scrotumLab/RadioMusic-for-BugBrand-FRAC/RadioMusic/SDPlayPCM.cpp

/* Audio Library for Teensy 3.X
 * Copyright (c) 2014, Paul Stoffregen, paul@pjrc.com
 *
 * Development of this audio library was funded by PJRC.COM, LLC by sales of
 * Teensy and Audio Adaptor boards.  Please support PJRC's efforts to develop
 * open source software by purchasing Teensy or other PJRC products.
 *
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
 * THE SOFTWARE IS PROVIDED "AS IS", WITHOUT WARRANTY OF ANY KIND, EXPRESS OR
 * IMPLIED, INCLUDING BUT NOT LIMITED TO THE WARRANTIES OF MERCHANTABILITY,
 * FITNESS FOR A PARTICULAR PURPOSE AND NONINFRINGEMENT. IN NO EVENT SHALL THE
 * AUTHORS OR COPYRIGHT HOLDERS BE LIABLE FOR ANY CLAIM, DAMAGES OR OTHER
 * LIABILITY, WHETHER IN AN ACTION OF CONTRACT, TORT OR OTHERWISE, ARISING FROM,
 * OUT OF OR IN CONNECTION WITH THE SOFTWARE OR THE USE OR OTHER DEALINGS IN
 * THE SOFTWARE.
 */

#include "SDPlayPCM.h"

#include "spi_interrupt.h"
#include "RadioMusic.h"

#ifdef DEBUG_PCM_PLAYER
#define D(x) x
#else
#define D(x)
#endif

#ifdef DEBUG_AUDIO_BUFFER
#define B(x) x
#else
#define B(x)
#endif


void SDPlayPCM::begin(void) {
//	AudioStartUsingSPI();
	playing = false;
	finished = false;
	errors = 0;
	// Set a dummy filename so it doesn't match anything at startup.
	filename = "--------";
}

void SDPlayPCM::loopPlayback(bool loop) {
	__disable_irq()
	;
	looping = loop;
	__enable_irq()
	;
}

bool SDPlayPCM::changeFileTo(AudioFileInfo* info, bool closeFirst) {
	filename = info->name;
//	AudioStopUsingSPI();
	__disable_irq()
	;
	if (closeFirst) {
		rawfile.close();
	}
	rawfile = SD.open(info->name.c_str());

	dataSize = info->size;
	bytesLeftInFile = info->size;
	dataOffset = info->dataOffset;
	channels = info->getChannels();
	bytesPerSample = info->getBytesPerSample();
	sampleRateSpeed = (float) info->getSampleRate() / 44100.0;
	bytesAvailable = 0;
	readPositionInBytes = 0;
	bufferFillPosition = 0;
	finished = false;
	readError = false;
	__enable_irq()
	;
//	AudioStartUsingSPI();
	D(
		if (dataSize % bytesPerSample != 0) {
			debugHeader();
			Serial.print("!!!! Data size not aligned : ");
			Serial.print(dataSize);
		}
		if(info->startPlayFrom != 0) {
			Serial.print("!!! Start play from is not 0 : ");
			Serial.println(info->startPlayFrom);
		}
		debugHeader();
		Serial.print("Change File To ");
		Serial.print(info->name);
		Serial.print(". BPS ");
		Serial.print(bytesPerSample);
		Serial.print(". BLIF ");
		Serial.print(bytesLeftInFile);
		Serial.print(" .SampleRateSpeed ");
		Serial.print(sampleRateSpeed);
		Serial.print(" .Bytes Per Block ");
		Serial.println(
				ceil(AUDIO_BLOCK_SAMPLES * speed * bytesPerSample * channels));
	);
	return true;
}

bool SDPlayPCM::skipTo(uint32_t dataPosition) {
	if(!rawfile) return false;
	uint32_t pos = dataOffset + dataPosition;
	AudioStopUsingSPI();
	__disable_irq()
	;
	boolean didseek = rawfile.seek(pos);
	bytesLeftInFile = dataSize - dataPosition;
	readPositionInBytes = 0;
	bytesAvailable = 0;
	bufferFillPosition = 0;
	readError = false;
	playing = true;
	finished = false;
	__enable_irq()
	;
	AudioStartUsingSPI();
	if(!didseek) {
		D(
			debugHeader();
			Serial.println("!!! didseek is false");
		);
		return false;
	}
	return true;
}

bool SDPlayPCM::playFrom(AudioFileInfo* info) {

	uint32_t pos = info->dataOffset + info->startPlayFrom;

	D(
		debugHeader();
		Serial.print("Play ");
		Serial.print(info->name);
		Serial.print(" from ");
		Serial.print(info->startPlayFrom);
		Serial.print(" starting from ");
		Serial.println(pos);
	);


	// We use the same file, just seek inside it.
	if (info->name.compareTo(filename) == 0) {
		D(
			debugHeader();
			Serial.print("Continuing on file ");
			Serial.print(filename);
			Serial.print(" from ");
			Serial.print(info->startPlayFrom);
			Serial.print(" of ");
			Serial.print(info->size);
			Serial.print(" with ");
			Serial.print(info->getBytesPerSample());
			Serial.print(" bps. File size ");
			Serial.println(rawfile.size());
		);

		updateRequired = false;
		return skipTo(info->startPlayFrom);

	} else {
		D(
			Serial.print("Different name ");
			Serial.println(filename);
		);
	}

	//if(playing) stop();

//	if(!playing) AudioStartUsingSPI();

	if (!changeFileTo(info, true)) {
		updateRequired = false;
		return false;
	} else {
		D(
			debugHeader();
			Serial.print("Change OK : ");
			Serial.println(rawfile.name());
		);
	}

	skipTo(info->startPlayFrom);

//	__disable_irq()
//	;
//	if(!rawfile.seek(pos)) {
//		debugHeader();
//		Serial.println("Seek failed");
//	}
//	bytesLeftInFile = info->size - info->startPlayFrom;
//	playing = true;
//	finished = false;
//	__enable_irq()
//	;

	D(
		debugHeader();
		Serial.print("Open. RPIB ");
		Serial.print(readPositionInBytes);
		Serial.print(" .InfoSize ");
		Serial.print(info->size);
		Serial.print(" .BLIF ");
		Serial.print(bytesLeftInFile);
		Serial.print(". File pos ");
		Serial.print(rawfile.position());
		Serial.print(". File size ");
		Serial.print(rawfile.size());
		Serial.print(". Avail ");
		Serial.println(fileAvailable());
	);
	updateRequired = false;
	return true;
}

void SDPlayPCM::restart() {

	D(
		debugHeader();
		Serial.println("Restart");
	);
	__disable_irq()
	;
	rawfile.seek(dataOffset);
	bytesLeftInFile = dataSize;
	playing = true;
	finished = false;
	__enable_irq()
	;
}

void SDPlayPCM::stop(void) {
	__disable_irq()
	;
	D(
		debugHeader();
		Serial.println("Stop");
	);
	if (playing) {
		playing = false;
		__enable_irq()
		;
//		AudioStopUsingSPI();
	} else {
		__enable_irq()
		;
	}
}

void SDPlayPCM::update(void) {

	uint16_t n = AUDIO_BLOCK_SAMPLES;
	audio_block_t *block;
	uint16_t i = 0;

	if(errors > 100) return;

	// only update if we're playing
	if (!playing)
		return;

	if(!looping) {
		if(finished || bytesLeftInFile == 0) {
			D(
				debugHeader();
				Serial.println("File finished");
			);
			playing = false;
			finished = true;
			return;
		}
	}

	// allocate the audio blocks to transmit
	block = allocate();
	if (block == NULL)
		return;

	inUpdate = true;
	read = 0;
	speed = playbackSpeed * sampleRateSpeed;
	bytesRequired = ceil(AUDIO_BLOCK_SAMPLES * speed) * bytesPerSample * channels;

	if (bytesRequired > AUDIOBUFSIZE) {
		bytesRequired = AUDIOBUFSIZE;
		D(
			debugHeader();
			Serial.println("!!! Bytes Required is bigger than the audio buffer..");
		);
	}

	if (bytesAvailable < bytesRequired) {

		bool bufferReadOk = false;
		if (bytesRequired
				< AUDIO_BLOCK_SAMPLES * bytesPerSample * channels) {
			bufferReadOk = fillBuffer(AUDIO_BLOCK_SAMPLES * bytesPerSample * channels);
		} else {
			bufferReadOk = fillBuffer(bytesRequired);
		}
B(
		if (read % bytesPerSample != 0) {
			debugHeader();
			Serial.print("Read not aligned ");
			Serial.print(read % bytesPerSample);
			Serial.print("\t");
			Serial.print(read);
			Serial.print("\t");
			Serial.println(bytesRequired);
		}
);

		if (read >= 0 && read < bytesRequired) {
			B(
				if (bytesAvailable % bytesPerSample != 0)
				{
					debugHeader();
					Serial.println("Bytes available not aligned");
				}

				if (read % bytesPerSample != 0) {
					debugHeader();
					Serial.print("Read not aligned ");
					Serial.print(read % bytesPerSample);
					Serial.print("\t");
					Serial.print(read);
					Serial.print("\t");
					Serial.println(bytesRequired);
				}
				if(!finished) {
					debugHeader();
					Serial.print("Not enough data from fill buffer ");
					Serial.print(bytesRequired);
					Serial.print("\t");
					Serial.print(bytesAvailable);
					Serial.print("\t");
					Serial.println(fileAvailable());
				} else {
					debugHeader();
					Serial.print("File finished ");
					Serial.print(bytesRequired);
					Serial.print("\t");
					Serial.print(bytesAvailable);
					Serial.print("\t");
					Serial.println(fileAvailable());
				}
			);
			n = min(AUDIO_BLOCK_SAMPLES,
					floor(bytesAvailable / (bytesPerSample * channels))	/ speed);
		} else if (readError || !bufferReadOk) {
			D(Serial.print("Read error. ");Serial.println(errors););
			errors++;
			readError = false;
			// Fill block with zero.
			for (i = 0; i < AUDIO_BLOCK_SAMPLES; i++) {
				block->data[i] = 0;
			}
			transmit(block);
			release(block);
			updates++;
			return;
		}

	}

	int16_t* out = block->data;

	l0 = 0;
	lowSamplePos = 0;
	float sp = speed * channels;

	// Check for buffer wrapping here so we don't do it 128 times in the loop.
	boolean bufferWrap = ((n*sp) * bytesPerSample) + readPositionInBytes >= AUDIOBUFSIZE;
	if (bytesPerSample == 2) {
		// 16 bit copy
		if(bufferWrap) {
			for (i = 0; i < n; i++) {
				lowSamplePos = (i * speed);
				l0 = readPositionInBytes + (lowSamplePos << channels);
				if (l0 >= AUDIOBUFSIZE) l0 -= AUDIOBUFSIZE;
				memcpy(out++, &audioBuffer[l0],2);
			}
		} else {
			// We won't wrap the buffer edge so don't check
			for (i = 0; i < n; i++) {
				lowSamplePos = (i * speed);
				l0 = readPositionInBytes + (lowSamplePos << channels);
				memcpy(out++, &audioBuffer[l0],2);
			}
		}
	} else if (bytesPerSample == 3) {

		if(channels == 1) {
			if(bufferWrap) {
				// 24 bit copy.
				for (i = 0; i < n; i++) {
					lowSamplePos = (i * speed);
					l0 = readPositionInBytes + (lowSamplePos * 3);
					if (l0 >= AUDIOBUFSIZE) l0 -= AUDIOBUFSIZE;
					*out++ = (audioBuffer[l0] | (audioBuffer[++l0] << 8) | (audioBuffer[++l0] << 16)) >> 8;
				}
			} else {
				// 24 bit copy.
				for (i = 0; i < n; i++) {
					lowSamplePos = (i * speed);
					l0 = readPositionInBytes + (lowSamplePos * 3);
					*out++ = (audioBuffer[l0] | (audioBuffer[++l0] << 8) | (audioBuffer[++l0] << 16)) >> 8;
				}
			}
		} else {
			if(bufferWrap) {
				// 24 bit copy.
				for (i = 0; i < n; i++) {
					lowSamplePos = (i * speed);
					l0 = readPositionInBytes + ((lowSamplePos * 3) << 1);
					if (l0 >= AUDIOBUFSIZE) l0 -= AUDIOBUFSIZE;
					*out++ = (audioBuffer[l0] | (audioBuffer[++l0] << 8) | (audioBuffer[++l0] << 16)) >> 8;
				}
			} else {
				// 24 bit copy.
				for (i = 0; i < n; i++) {
					lowSamplePos = (i * speed);
					l0 = readPositionInBytes + ((lowSamplePos * 3) << 1);
					*out++ = (audioBuffer[l0] | (audioBuffer[++l0] << 8) | (audioBuffer[++l0] << 16)) >> 8;
				}
			}

		}
	}

	if (n != AUDIO_BLOCK_SAMPLES) {
		B(
			debugHeader();
			Serial.print("n != BLOCK : ");
			Serial.println(n);
		);

		// There wasn't enough data earlier to fill the audio block

		bytesUsed = (n * sp) * bytesPerSample;
		// Fill rest of block with zeros.
		for (i = n; i < AUDIO_BLOCK_SAMPLES; i++) {
			*out++ = 0;
		}
		if (!looping)
			finished = true;
	} else {
		bytesUsed = bytesRequired;
	}

	readPositionInBytes += bytesUsed;
	readPositionInBytes %= AUDIOBUFSIZE;

	bytesAvailable -= bytesUsed;


	transmit(block);
	release(block);
	inUpdate = false;
	updates++;
	if(readError) errors++;
	readError = false;
}

bool SDPlayPCM::fillBuffer(int32_t requiredBytes) {

// How many bytes until the end of the buffer
	spaceLeftInBuffer = AUDIOBUFSIZE - bufferFillPosition;

	read = 0;

	int32_t read2 = 0;

	B(
		bool seekRequired = false;
		int seek = 0;
		int fillStyle = 0;

		uint32_t avail = fileAvailable();

		if(bytesLeftInFile > avail) {
			debugHeader();
			Serial.print("BLIF > Available at start. ");
			Serial.print(bytesLeftInFile);
			Serial.print(" > ");
			Serial.println(avail);
			if(bytesLeftInFile % bytesPerSample != 0) {
				Serial.println("BLIF not aligned");
			}
			if(avail % bytesPerSample != 0) {
				Serial.println("Available not aligned");
			} else {
				bytesLeftInFile = avail;
			}
		}
	);

	// Is there enough left to read from the file?
	if (bytesLeftInFile < requiredBytes - bytesAvailable) {
		B(
			debugHeader();
			Serial.print("Not enough data in file. ");
			Serial.print(bytesLeftInFile);
			Serial.print(" left. \t");
			Serial.print(bytesRequired);
			Serial.print(" Reqd\t");
			Serial.print(bytesAvailable);
			Serial.print(" avail after ");
			Serial.print(bufferFills);
			Serial.print(" fills. Left in buf ");
			Serial.println(spaceLeftInBuffer);
		);

		if (!looping) {
			// we're not looping and the file will run out
			// so only attempt to read the rest of the file
			B(
				debugHeader();
				Serial.print("Changing required to ");
				Serial.println(bytesLeftInFile);
			);
			requiredBytes = bytesLeftInFile;
		} else {
			B(
				debugHeader();
				Serial.println("Seek required during fillBuffer");
				seekRequired = true;
				seek = 1;
			);
		}
	}

	if (requiredBytes > spaceLeftInBuffer) {
		// If we read all the data we need it will go across the buffer boundary

		if (spaceLeftInBuffer <= bytesLeftInFile) {
			// Fill to end of buffer
			read = rawfile.read(&(audioBuffer[bufferFillPosition]),
					spaceLeftInBuffer);
			if (read == -1 && !readError) {
				B(
					Serial.println("SDP: Read Error 1");
				);
				readError = true;
				goto endfill;
			}
			bufferFillPosition = 0;

			if (requiredBytes <= bytesLeftInFile) {
				B(fillStyle = 1;);
				// Not enough buffer space, but enough left in file. No seek required
				// Fill buffer from start
				if (requiredBytes - read > 0) {
					read2 = rawfile.read(audioBuffer, requiredBytes - read);
					if (read2 == -1 && !readError) {
						readError = true;
						B(Serial.println("SDP: Read Error 2"););
						goto endfill;
					}
					read += read2;
					bufferFillPosition = read2;
				} else {
					bufferFillPosition = 0;
				}
				bytesLeftInFile -= read;

			} else {
				// There is enough data in the file to fill the end of the buffer
				// BUT NOT enough in the file to get all the data we need. Seek is required

				// We've already filled to the end of the buffer

				// now fill from start of buffer with what's left in the file
				if (bytesLeftInFile - read > 0) {
					read2 = rawfile.read(audioBuffer, bytesLeftInFile - read);
					if (read2 == -1 && !readError) {
						B(
							Serial.println("SDP: Read Error 3");
						);
						readError = true;
						goto endfill;
					}
					read += read2;
					bufferFillPosition = read2;
				}

				// Seek to start of file
				rawfile.seek(dataOffset);

				// get the bit thats left
				int32_t lastBit = requiredBytes - read;
				B(
					fillStyle = 2;
					seekRequired = true;
					seek = 0;

					if (lastBit <= 0) {
						Serial.print("SDP: Last bit not +ve ");
						Serial.println(lastBit);
					} else {
						debugHeader();
						Serial.print("Last bit ");
						Serial.println(lastBit);
					}
				);
				int32_t read3 = rawfile.read(&(audioBuffer[bufferFillPosition]),
						lastBit);
				if (read3 == -1 && !readError) {
					B(
						Serial.println("SDP: Read error 4");
					);
					readError = true;
					goto endfill;
				}


				read += read3;
				bytesLeftInFile = dataSize - lastBit;
				bufferFillPosition += lastBit;
			}
		} else {
			// Buffer has enough space to read the rest of the file.
			B(
				fillStyle = 3;
				seekRequired = true;
				seek = 0;
			);

			// Get the rest from the file
			read = rawfile.read(&(audioBuffer[bufferFillPosition]),
					bytesLeftInFile);
			if (read == -1 && !readError) {
				B(
					Serial.println("SDP: Read Error 5");
				);
				readError = true;
				goto endfill;
			}
			// go to start of file
			rawfile.seek(dataOffset);

			spaceLeftInBuffer -= read;

			// read to end of buffer
			read2 = rawfile.read(&(audioBuffer[bufferFillPosition + read]),
					spaceLeftInBuffer);
			if (read2 == -1 && !readError) {
				B(
					Serial.println("SDP: Read Error 6");
				);
				readError = true;
				goto endfill;
			}

			read += read2;

			// Fill buffer from start with amount that is left
			int32_t read3 = rawfile.read(audioBuffer, requiredBytes - read);
			if (read3 == -1 && !readError) {
				B(
					Serial.println("SDP: Read Error 7");
				);
				readError = true;
				goto endfill;
			}

			read += read3;
			bytesLeftInFile = dataSize - (read2 + read3);
			bufferFillPosition = read3;
		}
	} else {

		// There's enough space in the buffer, is there enough in the file
		if (bytesLeftInFile >= requiredBytes) {
//			Serial.println("Fill style 4.");
			// Enough in file, just read it
			read = rawfile.read(&(audioBuffer[bufferFillPosition]), requiredBytes);
			if (read == -1 && !readError) {
				B(
					fillStyle = 4;
					debugHeader();
					Serial.println("Read Error 8");
				);
				readError = true;
				goto endfill;
			} else {
				B(
					fillStyle = 4;
					if(read != requiredBytes) {
						debugHeader();
						Serial.print("Read != Required. BLIF ");
						Serial.print(bytesLeftInFile);
						Serial.print("\t File avail ");
						Serial.print(fileAvailable());
						Serial.print("\t File pos ");
						Serial.println(rawfile.position());
					}
				);
				bytesLeftInFile -= read;
				bufferFillPosition += read;
			}
		} else {

			// Not enough in file
			read = rawfile.read(&(audioBuffer[bufferFillPosition]),
					bytesLeftInFile);
			if (read == -1 && !readError) {
				B(
					fillStyle = 5;
					debugHeader();
					Serial.println("Read Error 9");
				);
				readError = true;
				goto endfill;
			}

			if (looping) {
				// If we're looping, seek back to start and fill from there
				rawfile.seek(dataOffset);

				read2 = rawfile.read(&(audioBuffer[bufferFillPosition + read]),
						requiredBytes - bytesLeftInFile);
				if (read2 == -1) {
					B(
						seekRequired = true;
						seek = 0;
						debugHeader();
						Serial.println("Read Error 10");
					);
					readError = true;
					goto endfill;
				}

				read += read2;
				bytesLeftInFile = dataSize - read2;
				bufferFillPosition += read;
			} else {
				// otherwise flag playback finished
				finished = true;
			}

		}
	}

	endfill:

	B(

		if(bytesLeftInFile > (fileAvailable())) {
			debugHeader();
			Serial.print("BLIF > AVAIL. ");
			Serial.print(bytesLeftInFile);
			Serial.print(" != ");
			Serial.print(fileAvailable());
			Serial.print(". Read ");
			Serial.print(read);
			Serial.print(". Style ");
			Serial.print(fillStyle);
			Serial.print(" Name. ");
			Serial.println(rawfile.name());
			Serial.print(". File Pos ");
			Serial.println(rawfile.position());
			if((fileAvailable()) % bytesPerSample == 0) {
				debugHeader();
				Serial.println("Avail2 not aligned");
			}
		}

		if(read == -1) {
			debugHeader();
			Serial.print("Read error. Fill style ");
			Serial.println(fillStyle);
			if(avail != (fileAvailable())) {
				debugHeader();
				Serial.print("Avail changed from ");
				Serial.print(avail);
				Serial.print(" to ");
				Serial.println(fileAvailable());
			}
		} else if(read > requiredBytes) {
			debugHeader();
			Serial.print("Read too much ");
			Serial.print(read);
			Serial.print(" wanted ");
			Serial.print(requiredBytes);
			Serial.print(" fill style was ");
			Serial.println(fillStyle);
		} else if(read < requiredBytes) {
			debugHeader();
			Serial.print("Didn't read enough ");
			Serial.print(read);
			Serial.print(" wanted ");
			Serial.print(requiredBytes);
			Serial.print(" fill style was ");
			Serial.println(fillStyle);
		}

		if(seekRequired) {
			if(seek) {
				debugHeader();
				Serial.print("Seek required but seek is high. ");
				Serial.print("Fill style ");
				Serial.println(fillStyle);
			} else {
				debugHeader();
				Serial.print("Seek completed. ");
				Serial.print("Fill style ");
				Serial.println(fillStyle);
			}
		}

	);

	if(read == -1 || readError) {
		return false;
	} else {
		bytesAvailable += read;
		bufferFillPosition %= AUDIOBUFSIZE;
		bufferFills++;
		if(bytesLeftInFile == 0) finished = true;
		return true;
	}
}

// Progress in file scaled from 0 to 1
float SDPlayPCM::offset(void) {
	// For now fudge it a bit and shift it forward in time by 2 blocks.
	uint32_t bytes = bytesLeftInFile <= (bytesRequired * 2) ? bytesLeftInFile : bytesLeftInFile - (bytesRequired * 2);
	float off = (float)(dataSize - bytes) / dataSize;
	D(
		debugHeader();
	Serial.print("Offset. Size ");
	Serial.print(dataSize);
	Serial.print("\t");
	Serial.print(bytesLeftInFile);
	Serial.print("\t");
	Serial.println(off,4);
	);
	return off;
}

// Note rawfile.available() is clamped to 16 bit signed int
// not sure why the SD library does that.
// Just do the same as SD does but don't clamp the result.
uint32_t SDPlayPCM::fileAvailable() {
	return rawfile.size() - rawfile.position();
}

void SDPlayPCM::debugHeader() {
	Serial.print("SDP:");
	Serial.print(playerID);
	Serial.write(' ');
}
