scrotumLab/RadioMusic-for-BugBrand-FRAC/RadioMusic/RadioMusic.h

#ifndef RadioMusic_h
#define RadioMusic_h

// Debug Flags
// #define DEBUG
//#define DEBUG_STARTUP
// #define DEBUG_SETTINGS
// #define DEBUG_INTERFACE
//#define DEBUG_WAV
//#define DEBUG_ENGINE
//#define DEBUG_FILES
//#define DEBUG_PCM_PLAYER
//#define DEBUG_AUDIO_BUFFER

// Regularly check CPU and Memory
//#define CHECK_CPU

// Test config modes
//#define TEST_RADIO_MODE
//#define TEST_DRUM_MODE

#endif
